johnbeardmore/oBeMS/Hardware/PCB Design/Schematics/15_10_6_oBeMs_PulsePCB_Schematic_Rev1.pdf

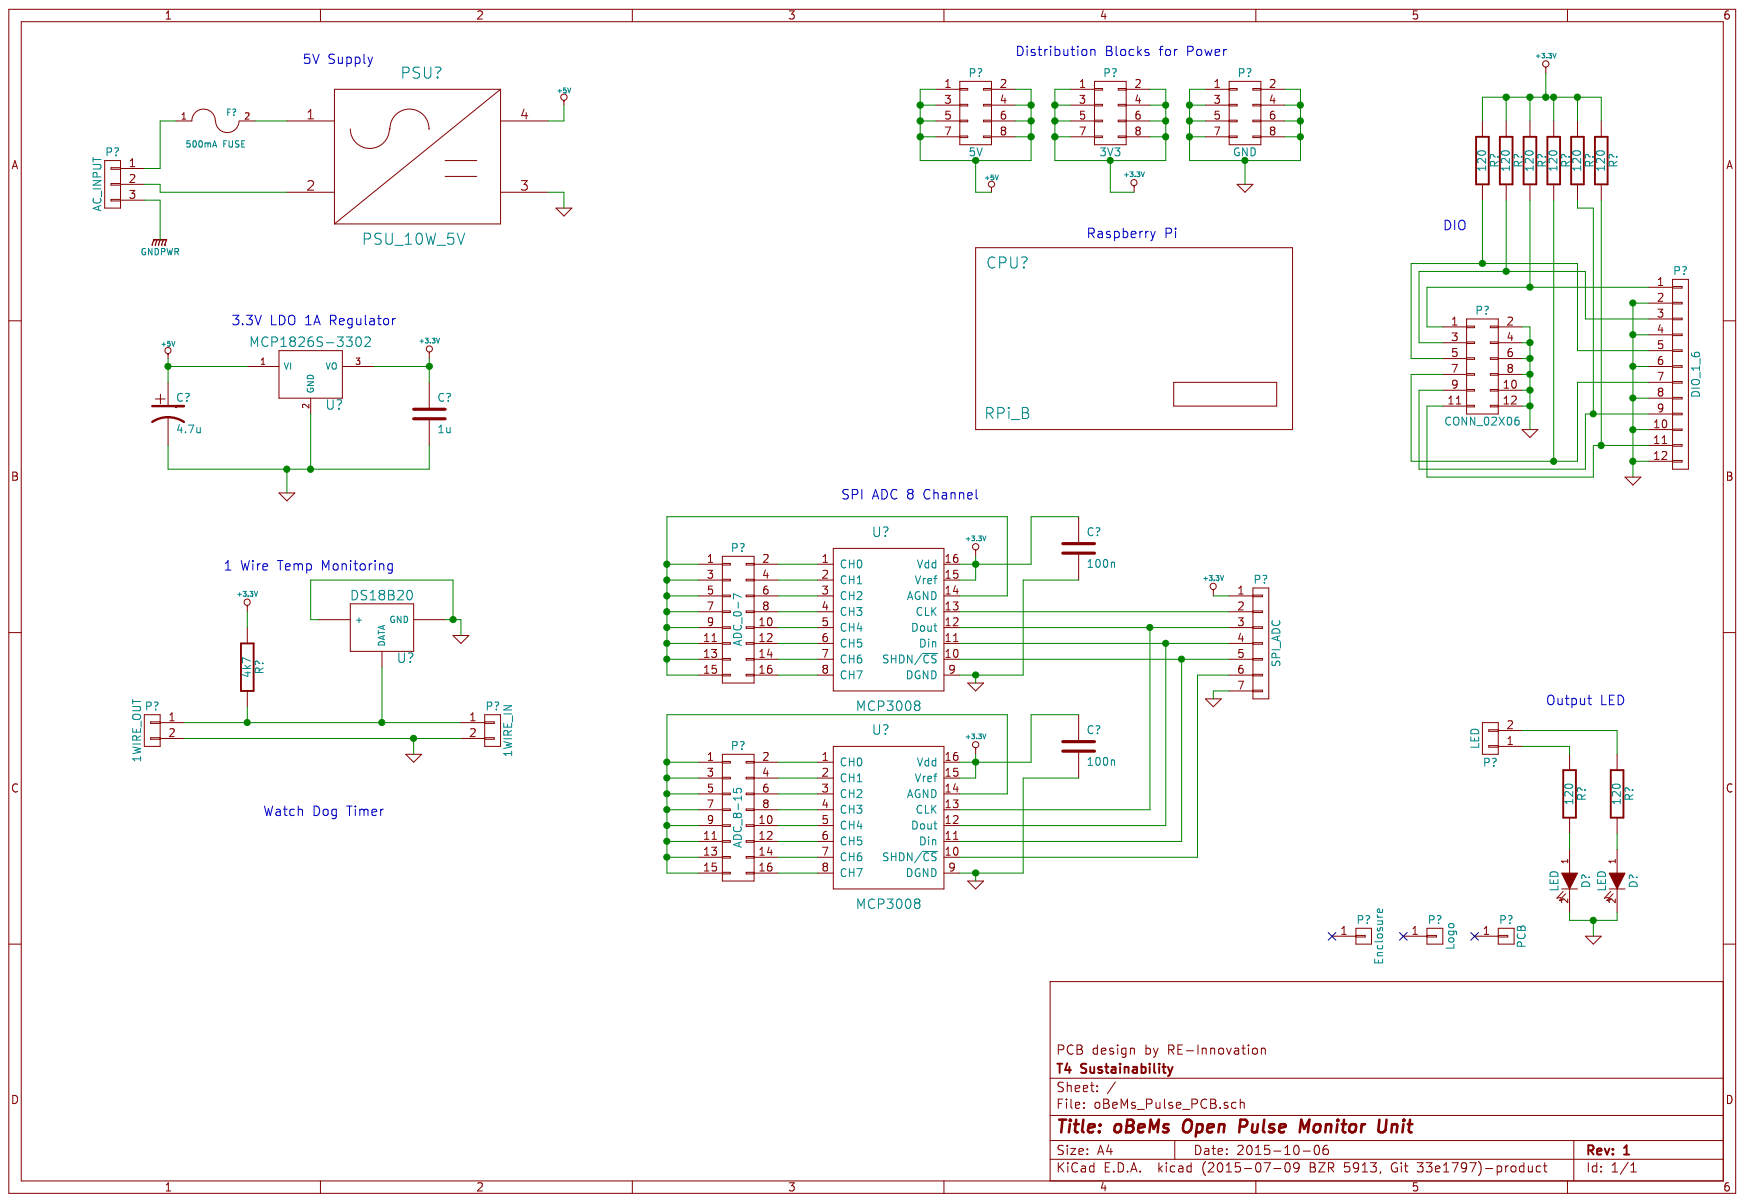
[picture p67: page 1]
